kberon/Mars-Rover/CAD Parts/Fixed CAD/Frame_C.SLDPRT

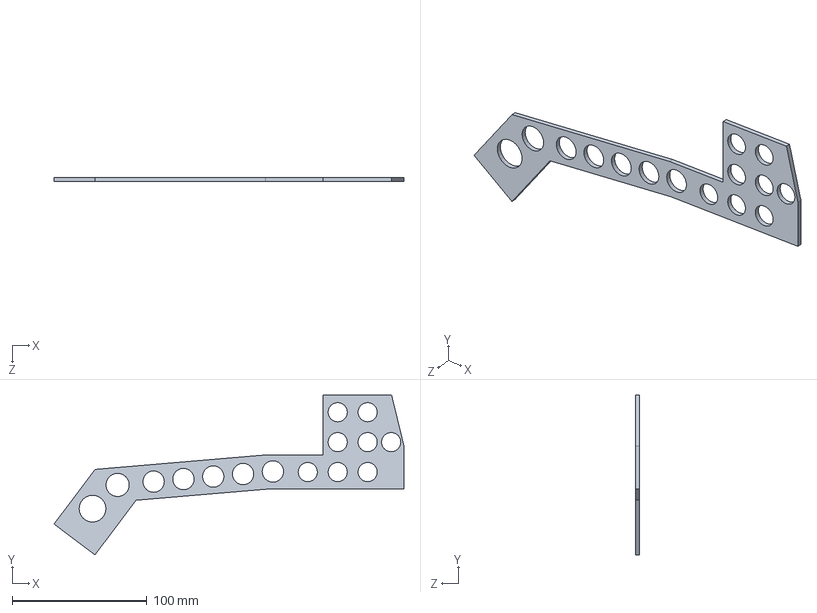
[picture p19: CAD file, 2024-02-22]
CAD Parts/Fixed CAD/Frame_C.SLDPRT
260.0 x 118.7 x 3.17 mm
