kberon/Mars-Rover/CAD Parts/New CAD/Shaft Coupler.SLDPRT

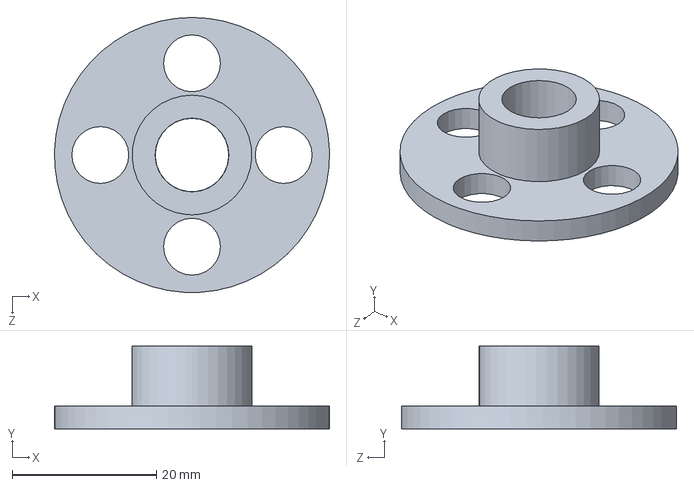
[picture p20: CAD file, 2024-03-21]
CAD Parts/New CAD/Shaft Coupler.SLDPRT
38.1 x 11.4 x 38.1 mm
