kberon/Mars-Rover/CAD Parts/Fixed CAD/Wheel.SLDPRT

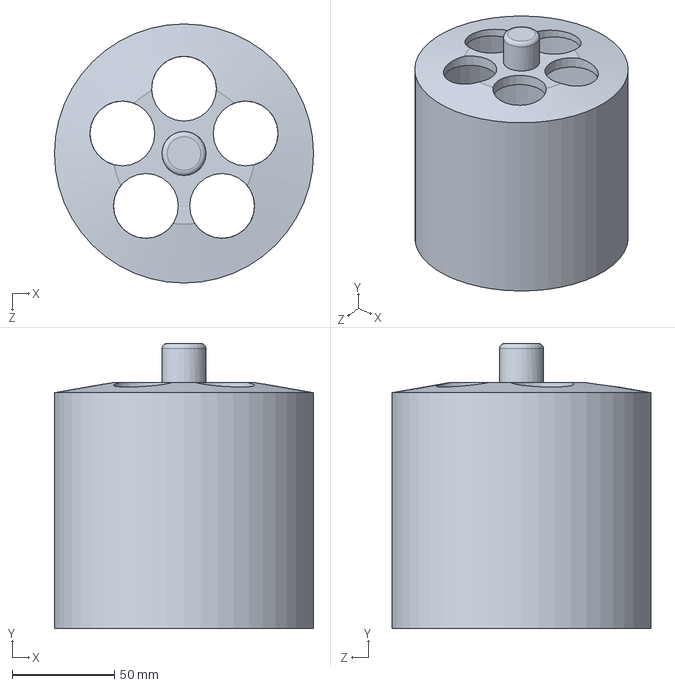
[picture p21: CAD file, 2024-02-22]
CAD Parts/Fixed CAD/Wheel.SLDPRT
127.0 x 139.7 x 127.0 mm
