kberon/Mars-Rover/CAD Parts/New CAD/Frame_Join_B.SLDPRT

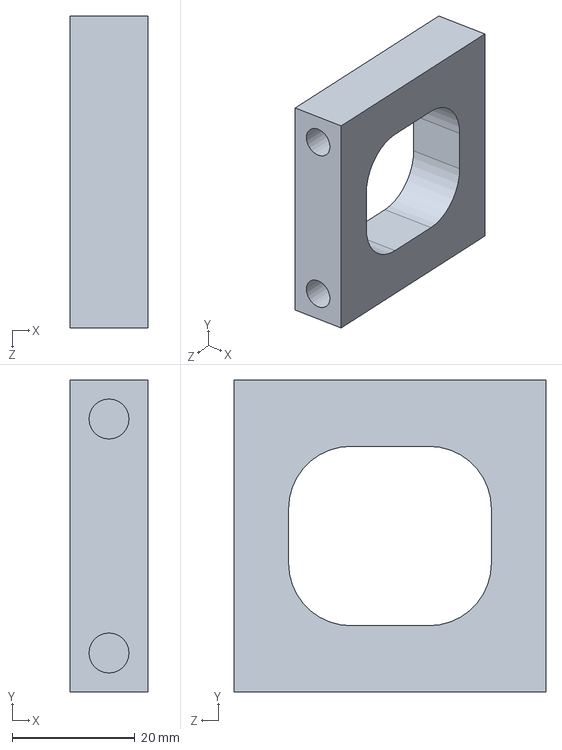
[picture p22: CAD file, 2024-03-21]
CAD Parts/New CAD/Frame_Join_B.SLDPRT
12.7 x 50.8 x 50.8 mm
