kberon/Mars-Rover/CAD Parts/Fixed CAD/Swerve_mount.SLDPRT

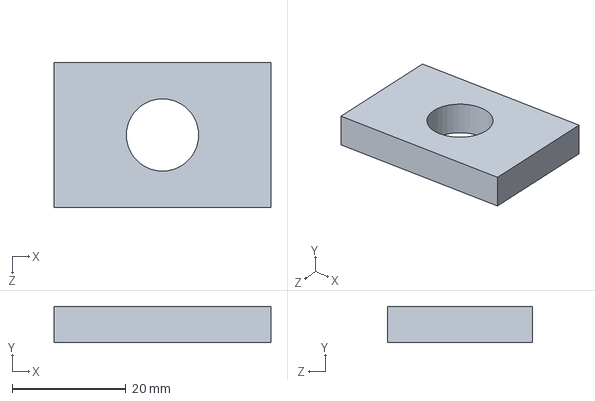
[picture p23: CAD file, 2024-02-22]
CAD Parts/Fixed CAD/Swerve_mount.SLDPRT
38.1 x 6.35 x 25.4 mm
