kberon/Mars-Rover/CAD Parts/Fixed CAD/0_75_in_shaft.SLDPRT

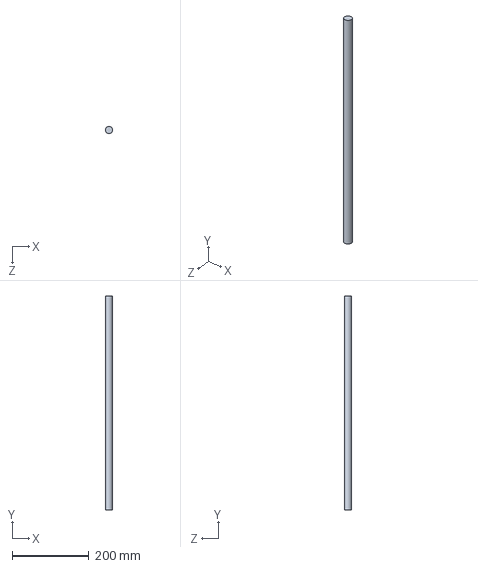
[picture p24: CAD file, 2024-02-22]
CAD Parts/Fixed CAD/0_75_in_shaft.SLDPRT
19.0 x 558.8 x 19.1 mm
