kberon/Mars-Rover/CAD Parts/Fixed CAD/0_5_in_shaft.SLDPRT

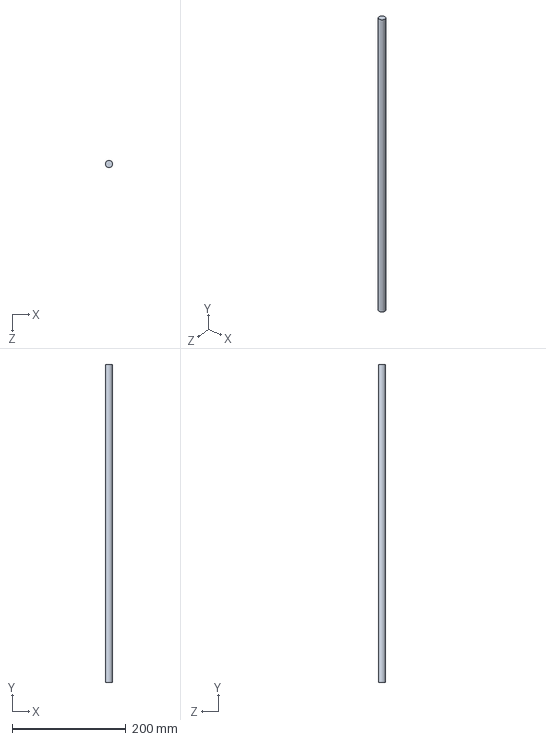
[picture p25: CAD file, 2024-02-22]
CAD Parts/Fixed CAD/0_5_in_shaft.SLDPRT
12.7 x 558.8 x 12.7 mm
