kberon/Mars-Rover/firmware/temp_motors/stop.py

import time
from adafruit_motorkit import MotorKit

kit = MotorKit()

kit.motor1.throttle = 0
kit.motor2.throttle = 0
kit.motor3.throttle = 0
kit.motor4.throttle = 0
